korjavin/skateholder/photos/deck_bottom.png

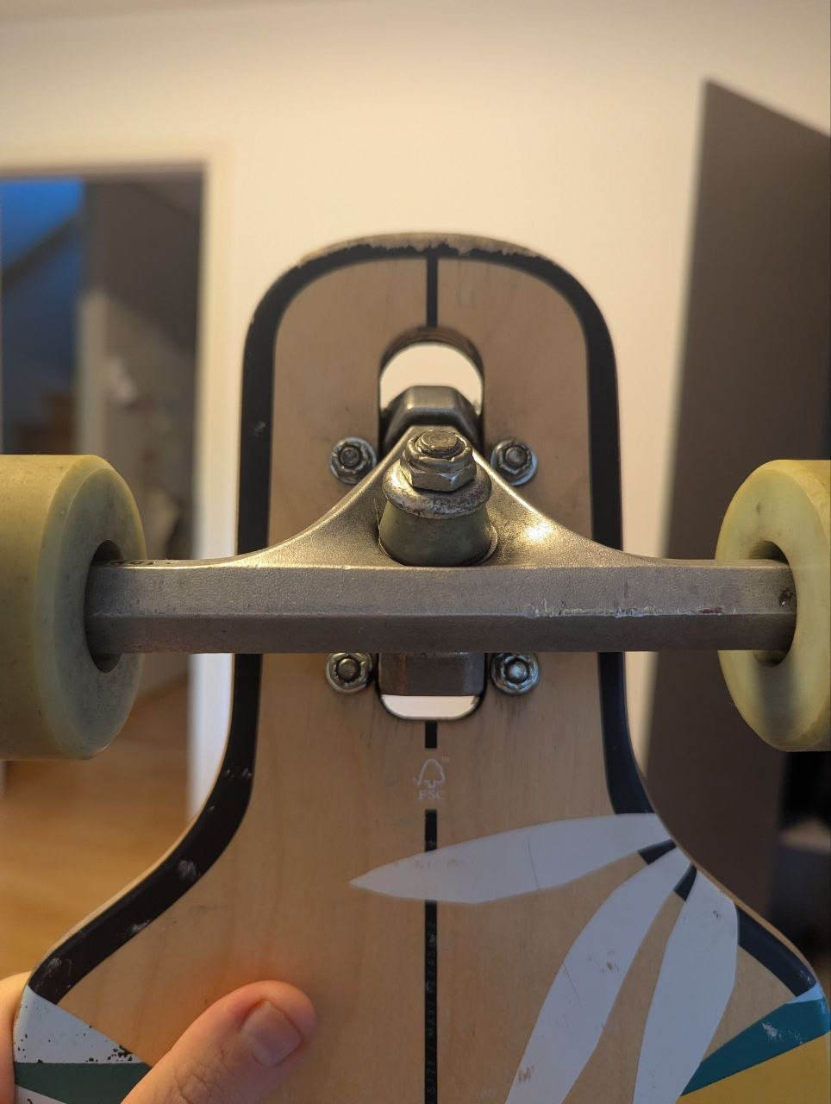
photos/deck_bottom.png
