korjavin/skateholder/renders/snap2_below.png

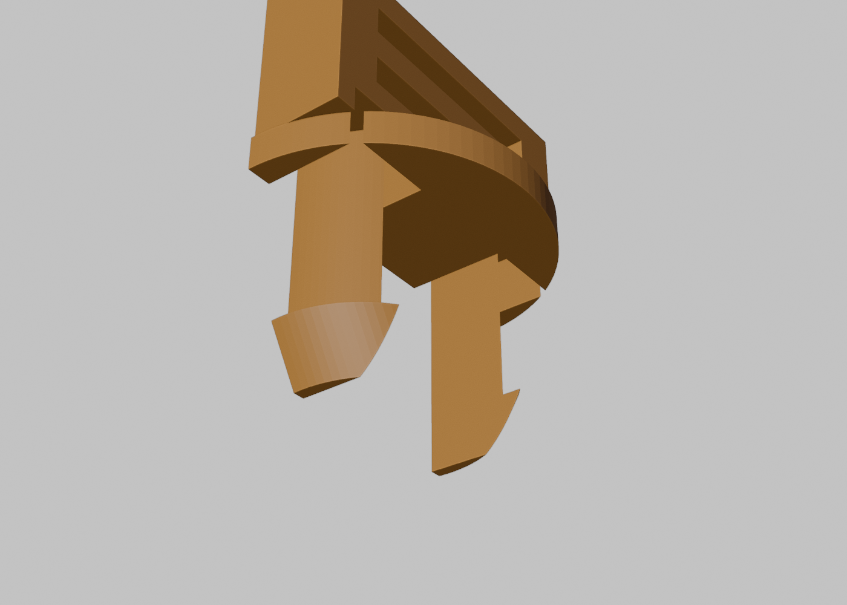
renders/snap2_below.png
