korjavin/skateholder/renders/snap2_on_deck.png

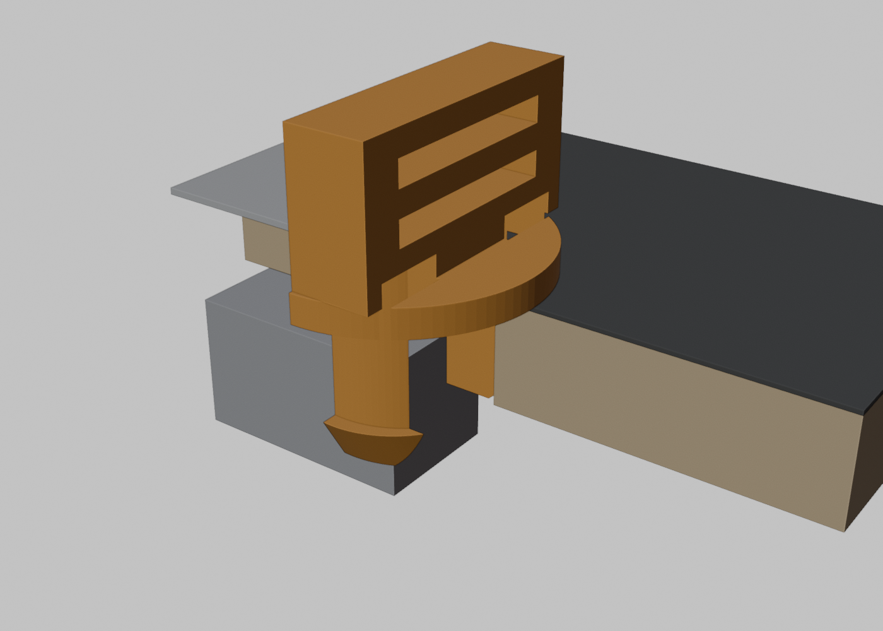
renders/snap2_on_deck.png
